promesoft/KicadJE-MidiToCV/P1040741.JPG

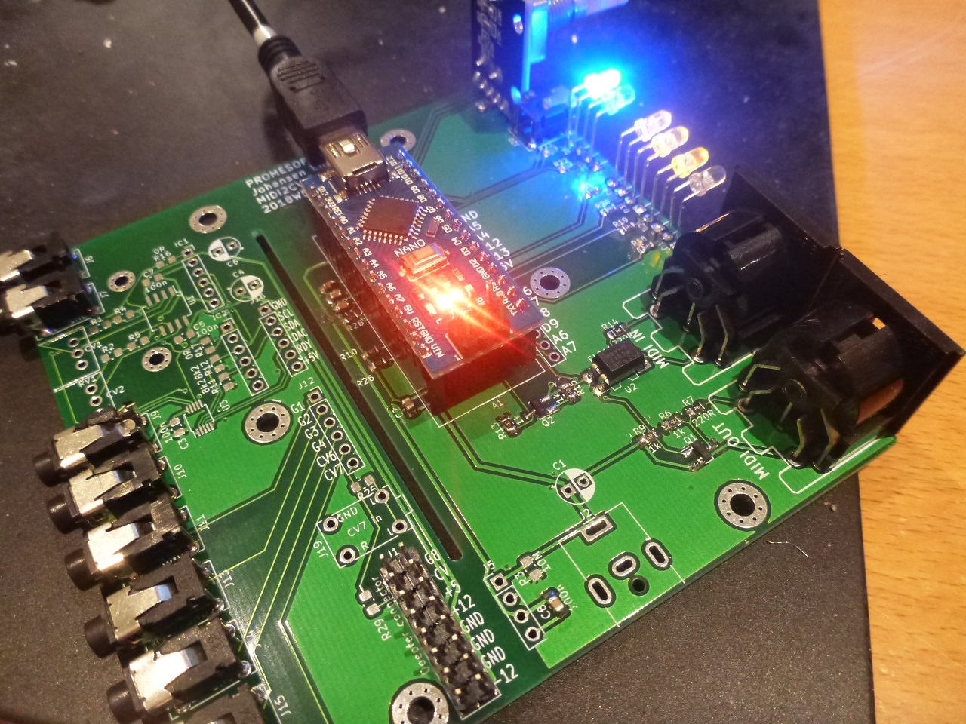
P1040741.JPG
