promesoft/KicadJE-MidiToCV/P1040744.JPG

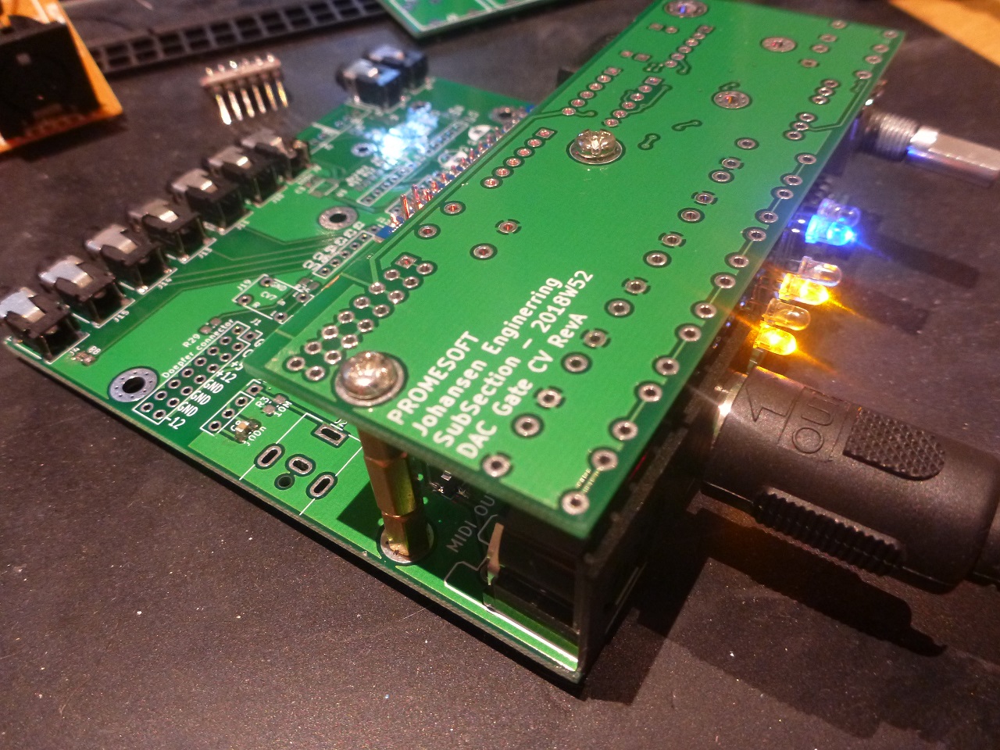
P1040744.JPG
