promesoft/KicadJE-MidiToCV/RevA/Kicad-Midi2CV-RevA_Bottom3D.png

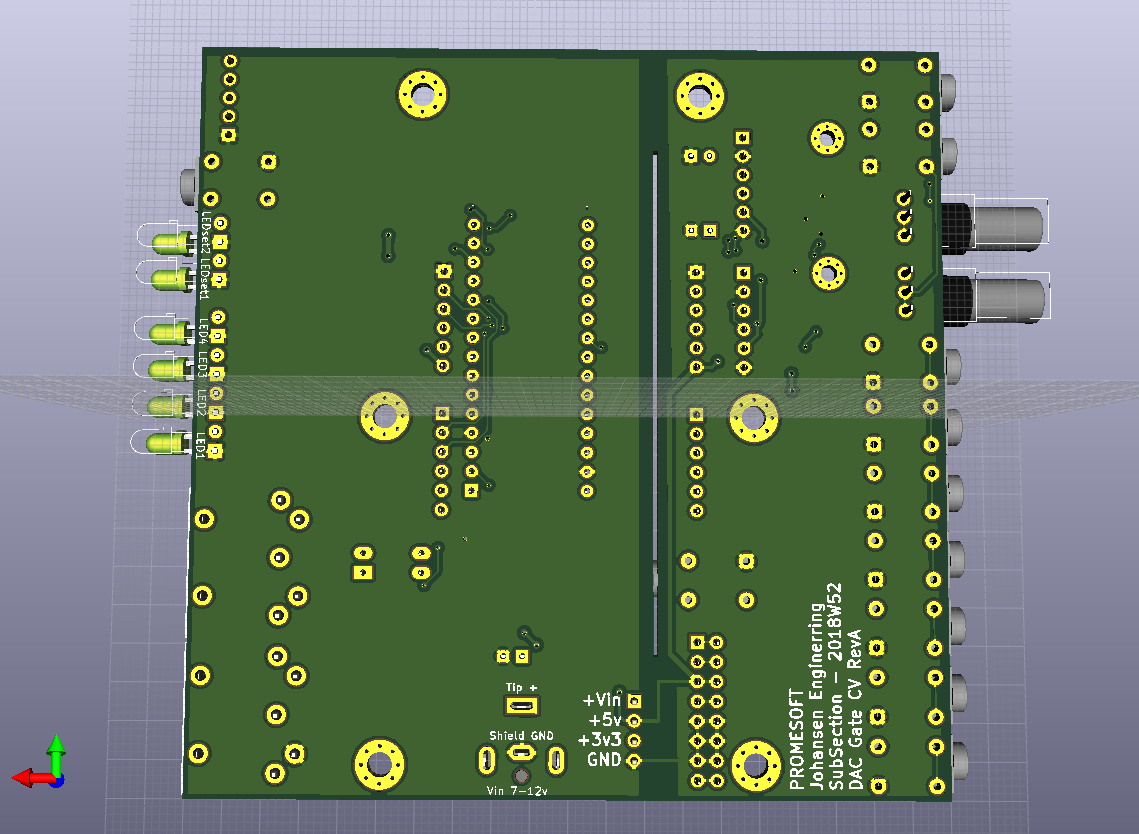
RevA/Kicad-Midi2CV-RevA_Bottom3D.png
