promesoft/KicadJE-MidiToCV/RevA/Kicad-Midi2CV-RevA_Top3D_2.png

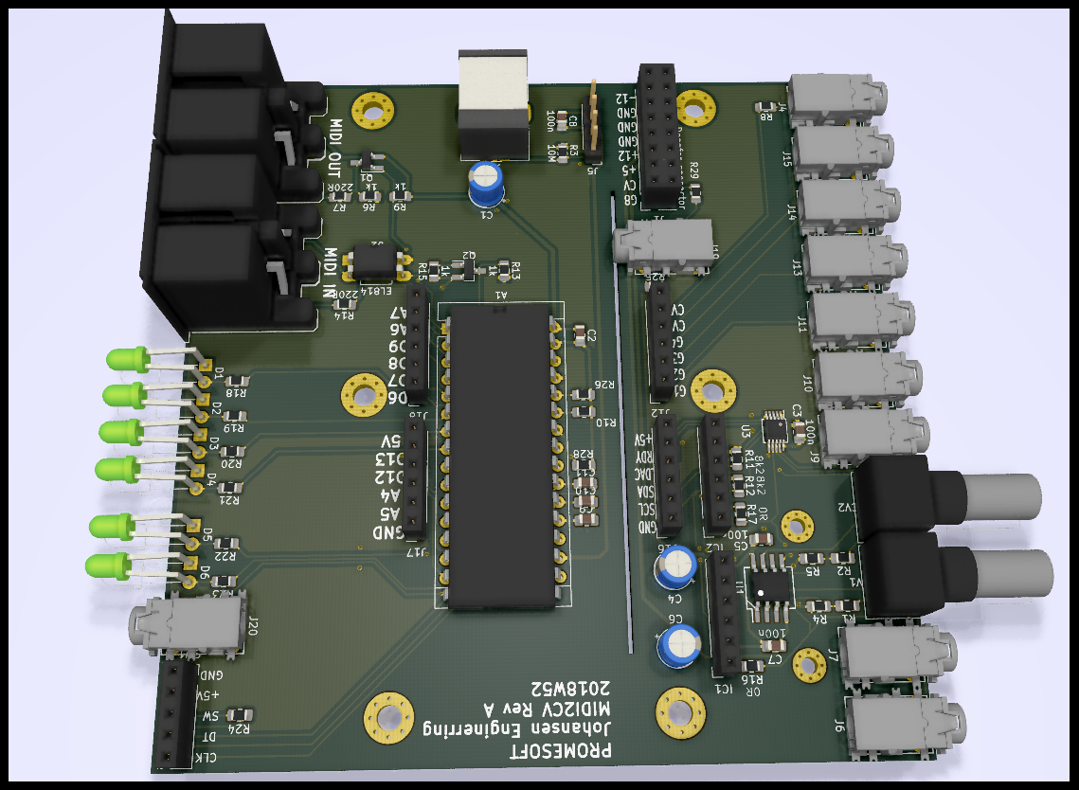
RevA/Kicad-Midi2CV-RevA_Top3D_2.png
